SigiMcArcel/CipedTronic/CipedTronicMcu2/sketch_CipedTronic/TimerCore.cpp

#include "esp32-hal-timer.h"
#include "TimerCore.h"

CipedTronic::TimerCore* CipedTronic::TimerCore::_Instance = NULL;

void IRAM_ATTR CipedTronic::TimerCore::onTimer(){
   portENTER_CRITICAL_ISR(&_Instance->_TimerMux);
    _Instance->_TimerTick++;
    portEXIT_CRITICAL_ISR(&_Instance->_TimerMux);
}



CipedTronic::TimerCore::TimerCore()
:_TimerMux(portMUX_INITIALIZER_UNLOCKED)
{
  
  _Timer = timerBegin(0, 80, true);
  timerAttachInterrupt(_Timer, &onTimer, true);
  timerAlarmWrite(_Timer, 1000, true);
   
}
  
CipedTronic::TimerCore* CipedTronic::TimerCore::Instance()
{
  if(CipedTronic::TimerCore::_Instance == NULL)
  {
      CipedTronic::TimerCore::_Instance = new CipedTronic::TimerCore; 
  }
  return CipedTronic::TimerCore::_Instance;
}

uint32_t CipedTronic::TimerCore::getTick()
{
  return _TimerTick;
}
  void CipedTronic::TimerCore::start()
  {
    timerAlarmEnable(_Timer);   
  }
  void CipedTronic::TimerCore::stop()
  {
      timerAlarmDisable(_Timer);
  }
