SigiMcArcel/CipedTronic/CipedTronicMcu/CipedTronicMCU/CipedTronic/utility/acilib.cpp

/* Copyright (c) 2010 Nordic Semiconductor. All Rights Reserved.
 *
 * The information contained herein is property of Nordic Semiconductor ASA.
 * Terms and conditions of usage are described in detail in NORDIC
 * SEMICONDUCTOR STANDARD SOFTWARE LICENSE AGREEMENT.
 *
 * Licensees are granted free, non-transferable use of the information. NO
 * WARRANTY of ANY KIND is provided. This heading must NOT be removed from
 * the file.
 *
 * $LastChangedRevision$
 */

/**
 * @file
 *
 * @ingroup group_acilib
 *
 * @brief Implementation of the acilib module.
 */

#include <string.h>
#include "hal_platform.h"
#include "aci.h"
#include "aci_cmds.h"
#include "aci_evts.h"
#include "acilib.h"
#include "aci_protocol_defines.h"
#include "acilib_defs.h"
#include "acilib_if.h"
#include "acilib_types.h"


void acil_encode_cmd_set_test_mode(uint8_t *buffer, aci_cmd_params_test_t *p_aci_cmd_params_test)
{
  *(buffer + OFFSET_ACI_CMD_T_LEN) = 2;
  *(buffer + OFFSET_ACI_CMD_T_CMD_OPCODE) = ACI_CMD_TEST;
  *(buffer + OFFSET_ACI_CMD_T_TEST + OFFSET_ACI_CMD_PARAMS_TEST_T_TEST_MODE_CHANGE) = p_aci_cmd_params_test->test_mode_change;
}

void acil_encode_cmd_sleep(uint8_t *buffer)
{
  *(buffer + OFFSET_ACI_CMD_T_LEN) = 1;
  *(buffer + OFFSET_ACI_CMD_T_CMD_OPCODE) = ACI_CMD_SLEEP;
}

void acil_encode_cmd_get_device_version(uint8_t *buffer)
{
  *(buffer + OFFSET_ACI_CMD_T_LEN) = 1;
  *(buffer + OFFSET_ACI_CMD_T_CMD_OPCODE) = ACI_CMD_GET_DEVICE_VERSION;
}

void acil_encode_cmd_set_local_data(uint8_t *buffer, aci_cmd_params_set_local_data_t *p_aci_cmd_params_set_local_data, uint8_t data_size)
{
  *(buffer + OFFSET_ACI_CMD_T_LEN) = MSG_SET_LOCAL_DATA_BASE_LEN + data_size;
  *(buffer + OFFSET_ACI_CMD_T_CMD_OPCODE) = ACI_CMD_SET_LOCAL_DATA;
  *(buffer + OFFSET_ACI_CMD_T_SET_LOCAL_DATA + OFFSET_ACI_CMD_PARAMS_SEND_DATA_T_TX_DATA + OFFSET_ACI_TX_DATA_T_PIPE_NUMBER) = p_aci_cmd_params_set_local_data->tx_data.pipe_number;
  memcpy(buffer + OFFSET_ACI_CMD_T_SET_LOCAL_DATA + OFFSET_ACI_CMD_PARAMS_SEND_DATA_T_TX_DATA + OFFSET_ACI_TX_DATA_T_ACI_DATA,  &(p_aci_cmd_params_set_local_data->tx_data._AciData[0]), data_size);
}

void acil_encode_cmd_connect(uint8_t *buffer, aci_cmd_params_connect_t *p_aci_cmd_params_connect)
{
  *(buffer + OFFSET_ACI_CMD_T_LEN) = MSG_CONNECT_LEN;
  *(buffer + OFFSET_ACI_CMD_T_CMD_OPCODE) = ACI_CMD_CONNECT;
  *(buffer + OFFSET_ACI_CMD_T_CONNECT + OFFSET_ACI_CMD_PARAMS_CONNECT_T_TIMEOUT_MSB) = (uint8_t)(p_aci_cmd_params_connect->timeout >> 8);
  *(buffer + OFFSET_ACI_CMD_T_CONNECT + OFFSET_ACI_CMD_PARAMS_CONNECT_T_TIMEOUT_LSB) = (uint8_t)(p_aci_cmd_params_connect->timeout);
  *(buffer + OFFSET_ACI_CMD_T_CONNECT + OFFSET_ACI_CMD_PARAMS_CONNECT_T_ADV_INTERVAL_MSB) = (uint8_t)(p_aci_cmd_params_connect->_AdvInterval >> 8);
  *(buffer + OFFSET_ACI_CMD_T_CONNECT + OFFSET_ACI_CMD_PARAMS_CONNECT_T_ADV_INTERVAL_LSB) = (uint8_t)(p_aci_cmd_params_connect->_AdvInterval);
}

void acil_encode_cmd_bond(uint8_t *buffer, aci_cmd_params_bond_t *p_aci_cmd_params_bond)
{
  *(buffer + OFFSET_ACI_CMD_T_LEN) = MSG_BOND_LEN;
  *(buffer + OFFSET_ACI_CMD_T_CMD_OPCODE) = ACI_CMD_BOND;
  *(buffer + OFFSET_ACI_CMD_T_BOND + OFFSET_ACI_CMD_PARAMS_BOND_T_TIMEOUT_MSB) = (uint8_t)(p_aci_cmd_params_bond->timeout >> 8);
  *(buffer + OFFSET_ACI_CMD_T_BOND + OFFSET_ACI_CMD_PARAMS_BOND_T_TIMEOUT_LSB) = (uint8_t)(p_aci_cmd_params_bond->timeout);
  *(buffer + OFFSET_ACI_CMD_T_BOND + OFFSET_ACI_CMD_PARAMS_BOND_T_ADV_INTERVAL_MSB) = (uint8_t)(p_aci_cmd_params_bond->_AdvInterval >> 8);
  *(buffer + OFFSET_ACI_CMD_T_BOND + OFFSET_ACI_CMD_PARAMS_BOND_T_ADV_INTERVAL_LSB) = (uint8_t)(p_aci_cmd_params_bond->_AdvInterval);
}

void acil_encode_cmd_disconnect(uint8_t *buffer, aci_cmd_params_disconnect_t *p_aci_cmd_params_disconnect)
{
  *(buffer + OFFSET_ACI_CMD_T_LEN) = MSG_DISCONNECT_LEN;
  *(buffer + OFFSET_ACI_CMD_T_CMD_OPCODE) = ACI_CMD_DISCONNECT;
  *(buffer + OFFSET_ACI_CMD_T_DISCONNECT + OFFSET_ACI_CMD_PARAMS_DISCONNECT_T_REASON) = (uint8_t)(p_aci_cmd_params_disconnect->reason);
}

void acil_encode_baseband_reset(uint8_t *buffer)
{
  *(buffer + OFFSET_ACI_CMD_T_LEN) = MSG_BASEBAND_RESET_LEN;
  *(buffer + OFFSET_ACI_CMD_T_CMD_OPCODE) = ACI_CMD_RADIO_RESET;
}

void acil_encode_direct_connect(uint8_t *buffer)
{
  *(buffer + OFFSET_ACI_CMD_T_LEN) = MSG_DIRECT_CONNECT_LEN;
  *(buffer + OFFSET_ACI_CMD_T_CMD_OPCODE) = ACI_CMD_CONNECT_DIRECT;
}

void acil_encode_cmd_wakeup(uint8_t *buffer)
{
  *(buffer + OFFSET_ACI_CMD_T_LEN) = MSG_WAKEUP_LEN;
  *(buffer + OFFSET_ACI_CMD_T_CMD_OPCODE) = ACI_CMD_WAKEUP;
}

void acil_encode_cmd_set_radio_tx_power(uint8_t *buffer, aci_cmd_params_set_tx_power_t *p_aci_cmd_params_set_tx_power)
{
  *(buffer + OFFSET_ACI_CMD_T_LEN) = MSG_SET_RADIO_TX_POWER_LEN;
  *(buffer + OFFSET_ACI_CMD_T_CMD_OPCODE) = ACI_CMD_SET_TX_POWER;
  *(buffer + OFFSET_ACI_CMD_T_SET_TX_POWER + OFFSET_ACI_CMD_PARAMS_SET_TX_POWER_T_DEVICE_POWER) = (uint8_t)p_aci_cmd_params_set_tx_power->device_power;
}

void acil_encode_cmd_get_address(uint8_t *buffer)
{
  *(buffer + OFFSET_ACI_CMD_T_LEN) = MSG_GET_DEVICE_ADDR_LEN;
  *(buffer + OFFSET_ACI_CMD_T_CMD_OPCODE) = ACI_CMD_GET_DEVICE_ADDRESS;
}

void acil_encode_cmd_send_data(uint8_t *buffer, aci_cmd_params_send_data_t *p_aci_cmd_params_send_data_t, uint8_t data_size)
{
  *(buffer + OFFSET_ACI_CMD_T_LEN) = MSG_SEND_DATA_BASE_LEN + data_size;
  *(buffer + OFFSET_ACI_CMD_T_CMD_OPCODE) = ACI_CMD_SEND_DATA;
  *(buffer + OFFSET_ACI_CMD_T_SEND_DATA + OFFSET_ACI_CMD_PARAMS_SEND_DATA_T_TX_DATA + OFFSET_ACI_TX_DATA_T_PIPE_NUMBER) = p_aci_cmd_params_send_data_t->tx_data.pipe_number;
  memcpy((buffer + OFFSET_ACI_CMD_T_SEND_DATA + OFFSET_ACI_CMD_PARAMS_SEND_DATA_T_TX_DATA + OFFSET_ACI_TX_DATA_T_ACI_DATA), &(p_aci_cmd_params_send_data_t->tx_data._AciData[0]), data_size);
}

void acil_encode_cmd_request_data(uint8_t *buffer, aci_cmd_params_request_data_t *p_aci_cmd_params_request_data)
{
  *(buffer + OFFSET_ACI_CMD_T_LEN) = MSG_DATA_REQUEST_LEN;
  *(buffer + OFFSET_ACI_CMD_T_CMD_OPCODE) = ACI_CMD_REQUEST_DATA;
  *(buffer + OFFSET_ACI_CMD_T_REQUEST_DATA + OFFSET_ACI_CMD_PARAMS_REQUEST_DATA_T_PIPE_NUMBER) = p_aci_cmd_params_request_data->pipe_number;
}

void acil_encode_cmd_open_remote_pipe(uint8_t *buffer, aci_cmd_params_open_remote_pipe_t *p_aci_cmd_params_open_remote_pipe)
{
  *(buffer + OFFSET_ACI_CMD_T_LEN) = MSG_OPEN_REMOTE_PIPE_LEN;
  *(buffer + OFFSET_ACI_CMD_T_CMD_OPCODE) = ACI_CMD_OPEN_REMOTE_PIPE;
  *(buffer + OFFSET_ACI_CMD_T_OPEN_REMOTE_PIPE + OFFSET_ACI_CMD_PARAMS_OPEN_REMOTE_PIPE_T_PIPE_NUMBER) = p_aci_cmd_params_open_remote_pipe->pipe_number;
}

void acil_encode_cmd_close_remote_pipe(uint8_t *buffer, aci_cmd_params_close_remote_pipe_t *p_aci_cmd_params_close_remote_pipe)
{
  *(buffer + OFFSET_ACI_CMD_T_LEN) = MSG_CLOSE_REMOTE_PIPE_LEN;
  *(buffer + OFFSET_ACI_CMD_T_CMD_OPCODE) = ACI_CMD_CLOSE_REMOTE_PIPE;
  *(buffer + OFFSET_ACI_CMD_T_CLOSE_REMOTE_PIPE + OFFSET_ACI_CMD_PARAMS_CLOSE_REMOTE_PIPE_T_PIPE_NUMBER) = p_aci_cmd_params_close_remote_pipe->pipe_number;
}

void acil_encode_cmd_echo_msg(uint8_t *buffer, aci_cmd_params_echo_t *p_cmd_params_echo, uint8_t msg_size)
{
  *(buffer + OFFSET_ACI_CMD_T_LEN) = MSG_ECHO_MSG_CMD_BASE_LEN + msg_size;
  *(buffer + OFFSET_ACI_CMD_T_CMD_OPCODE) = ACI_CMD_ECHO;
  memcpy((buffer + OFFSET_ACI_CMD_T_ECHO + OFFSET_ACI_CMD_PARAMS_ECHO_T_ECHO_DATA), &(p_cmd_params_echo->echo_data[0]), msg_size);
}
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
